NdK73/HomeAutomation/domoswitch/DomoSwitch-panelized-gerbers/DomoSwitch-1_Bottom.png

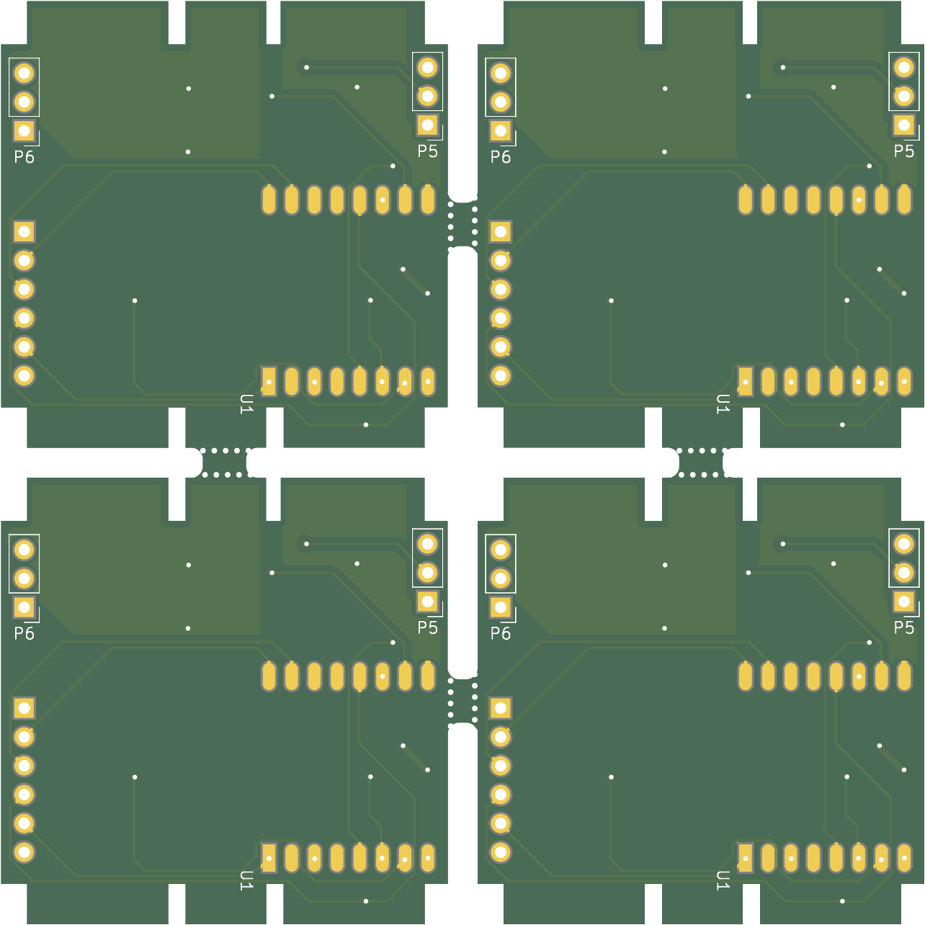
domoswitch/DomoSwitch-panelized-gerbers/DomoSwitch-1_Bottom.png
