NdK73/HomeAutomation/domoswitch/DomoSwitch-panelized-gerbers/DomoSwitch-3_Bottom.png

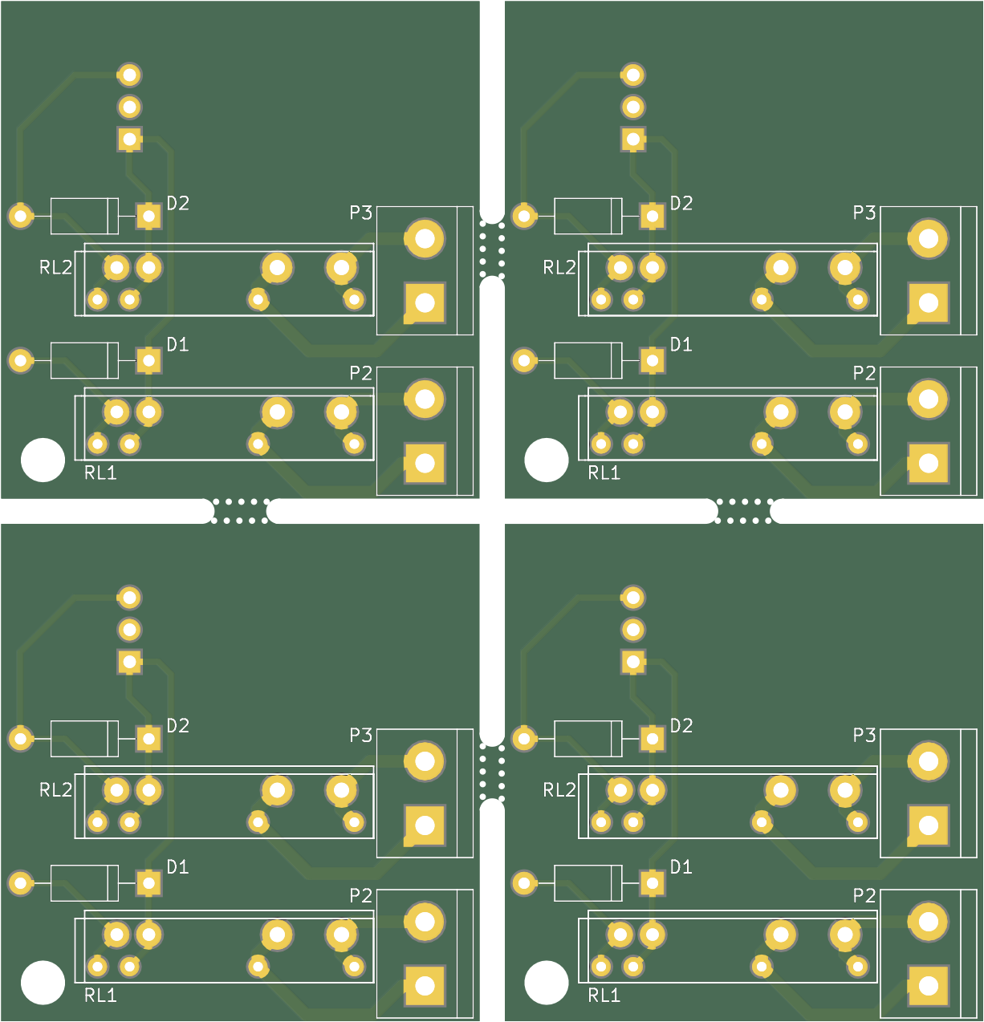
domoswitch/DomoSwitch-panelized-gerbers/DomoSwitch-3_Bottom.png
