NdK73/HomeAutomation/domonode/domonode.pdf

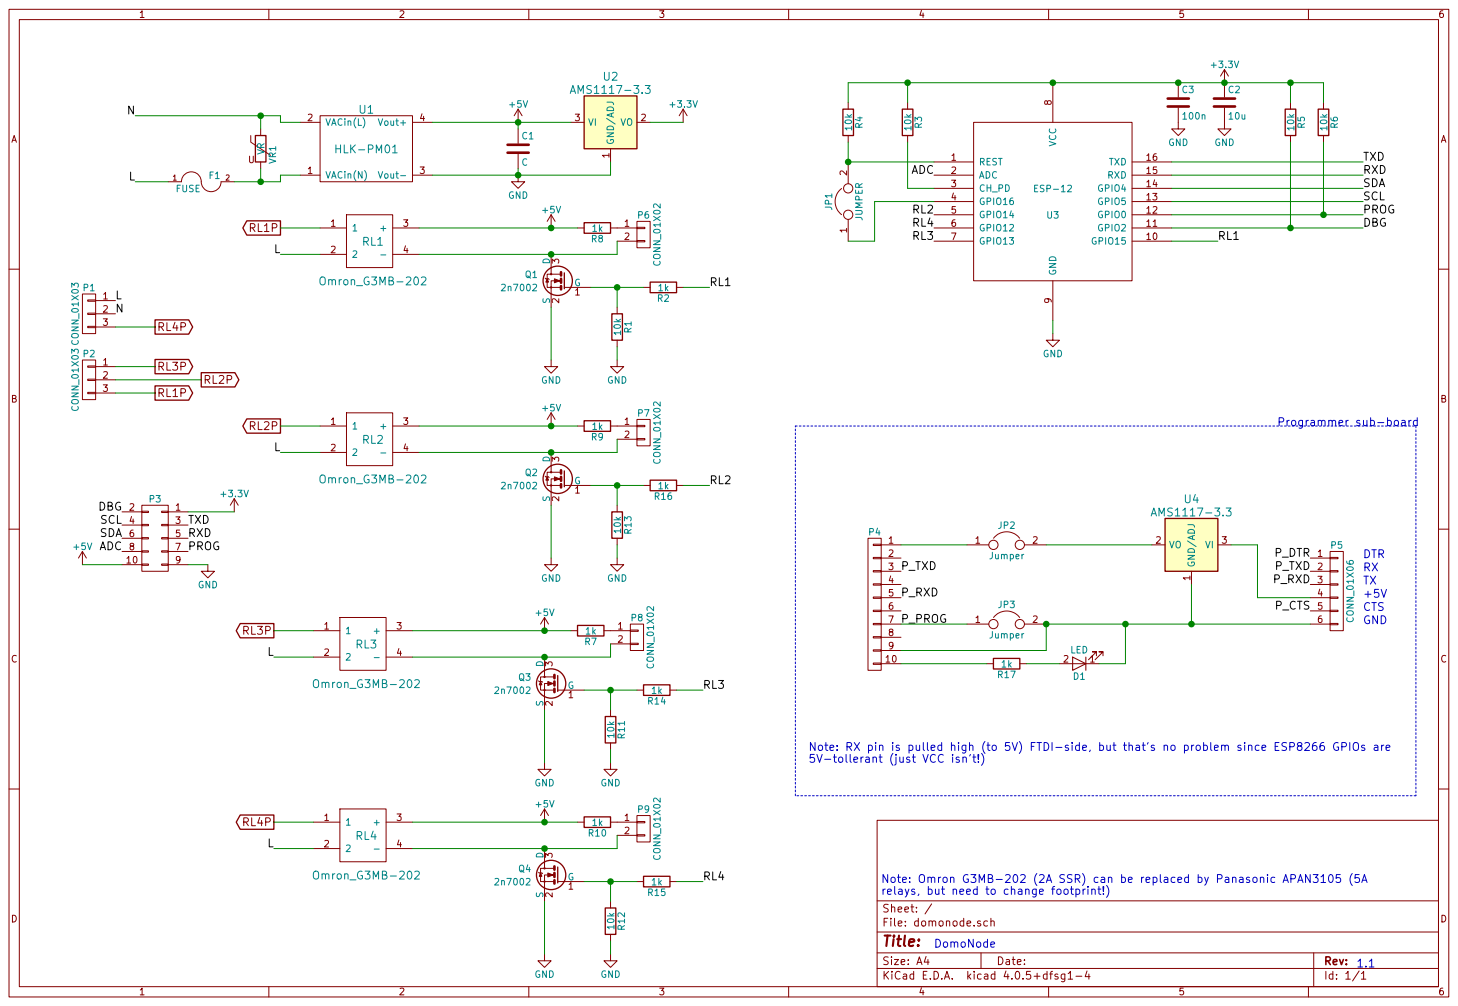
[picture p13: page 1]

relays, but need to change footprint!) 123456789

LED Note: RX pin is pulled high (to 5V) FTDI-side, but that's no problem since ESP8266 GPIOs are

5V-tollerant (just VCC isn't!)

Note: Omron G3MB-202 (2A SSR) can be replaced by Panasonic APAN3105 (5A

Id: 1/1 Title: File: domonode.sch Sheet: /
